sci-bots/dropbot-v3/docs/images/png/MicroDrop screenshots/MicroDrop left pane - green.png

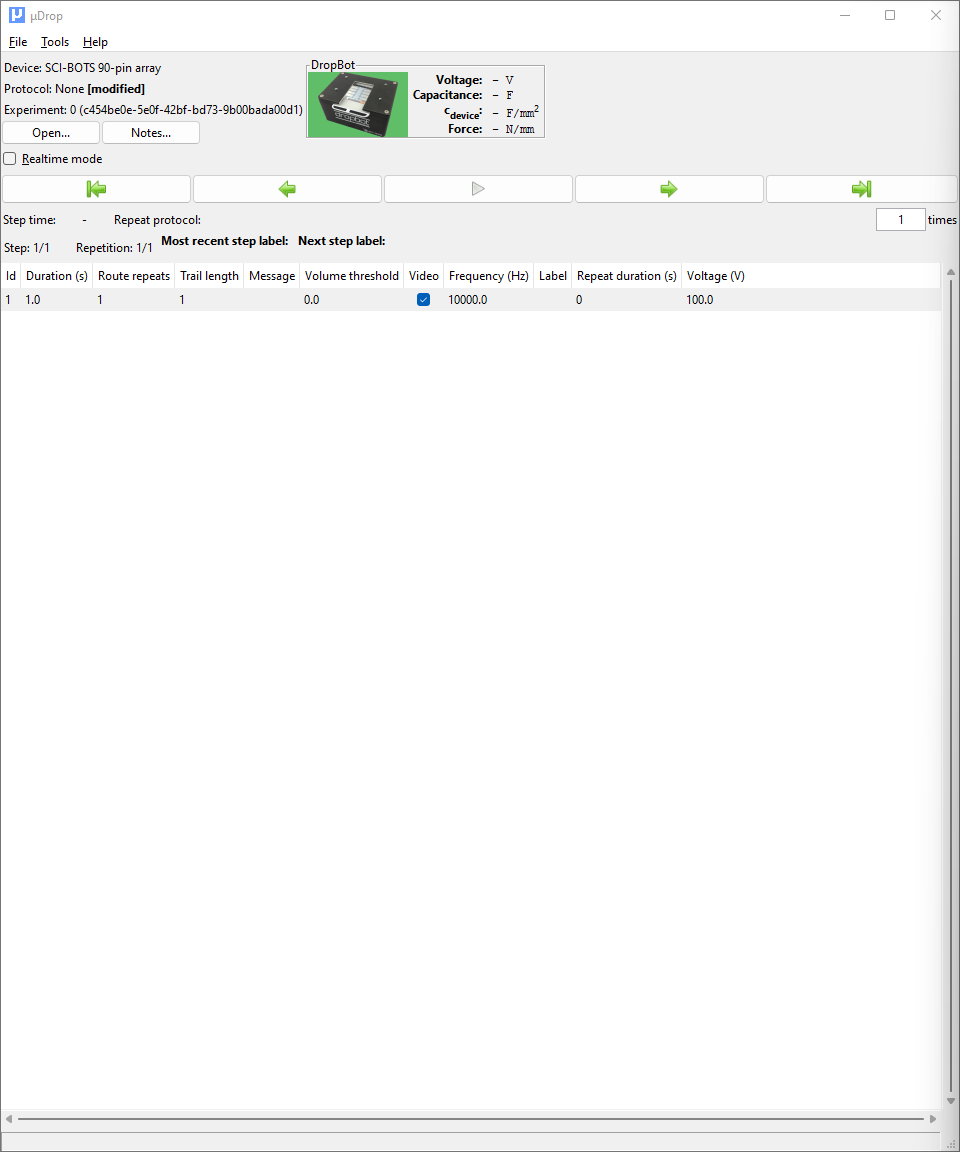
docs/images/png/MicroDrop screenshots/MicroDrop left pane - green.png
