sci-bots/dropbot-v3/docs/images/png/MicroDrop screenshots/MicroDrop left pane - yellow.png

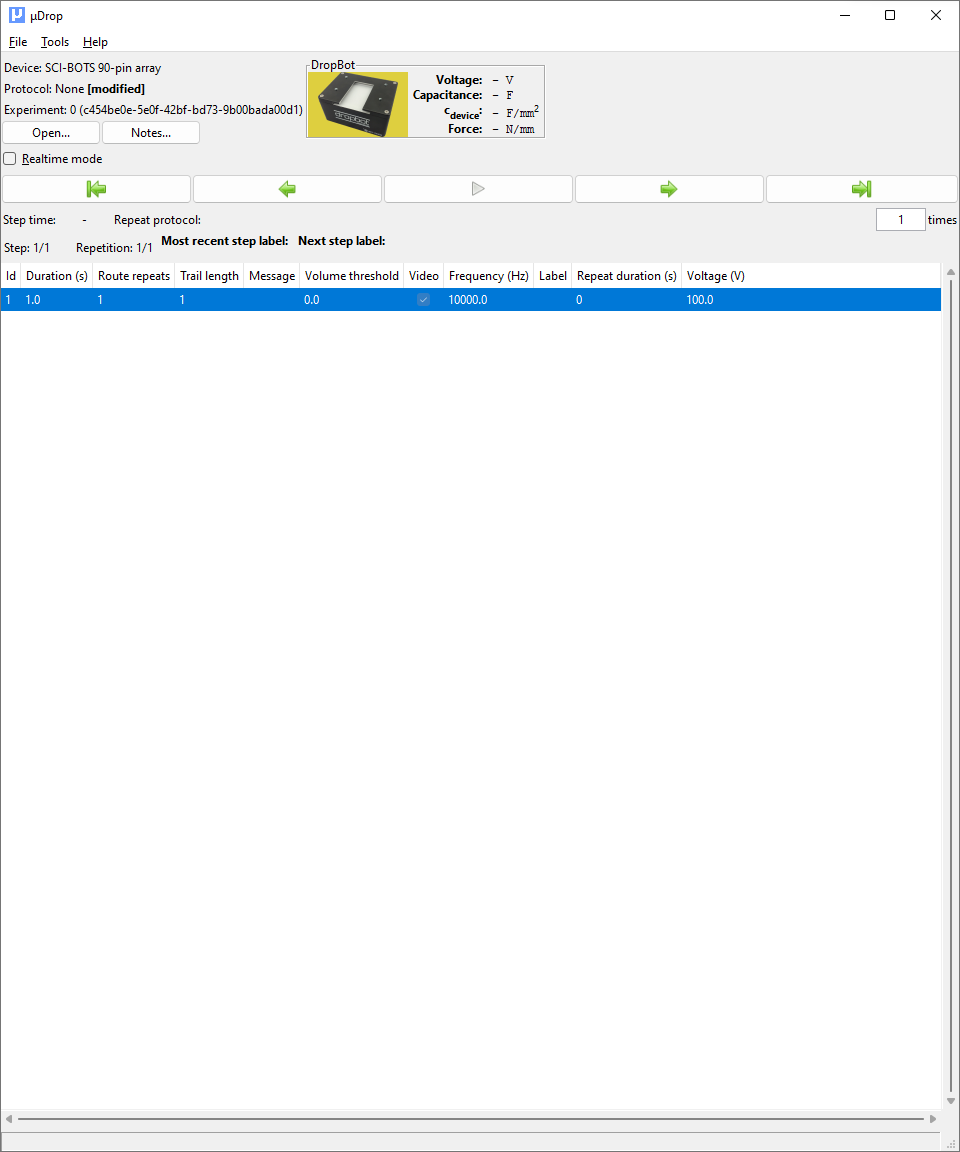
docs/images/png/MicroDrop screenshots/MicroDrop left pane - yellow.png
