sci-bots/dropbot-v3/docs/images/png/MicroDrop screenshots/Teensy1.png

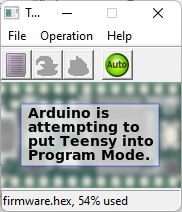
docs/images/png/MicroDrop screenshots/Teensy1.png
