sci-bots/dropbot-v3/docs/images/png/MicroDrop screenshots/Teensy2.png

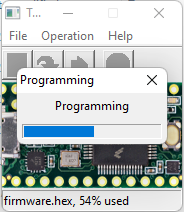
docs/images/png/MicroDrop screenshots/Teensy2.png
