sci-bots/dropbot-v3/docs/images/png/MicroDrop screenshots/Teensy3.png

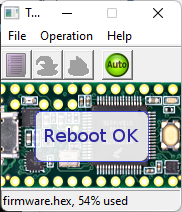
docs/images/png/MicroDrop screenshots/Teensy3.png
