sci-bots/dropbot-v3/docs/images/jpg/Assembly pictures/PXL_20220801_192833574.jpg

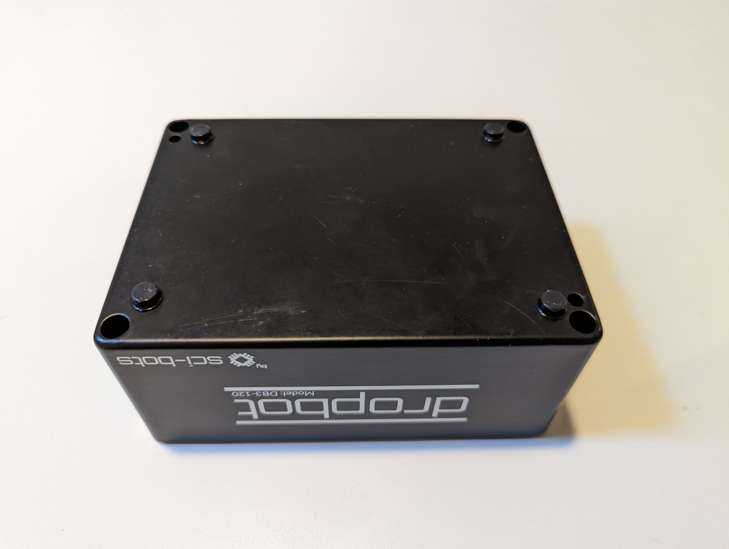
docs/images/jpg/Assembly pictures/PXL_20220801_192833574.jpg
