sci-bots/dropbot-v3/docs/images/jpg/Assembly pictures/PXL_20220801_195305338.jpg

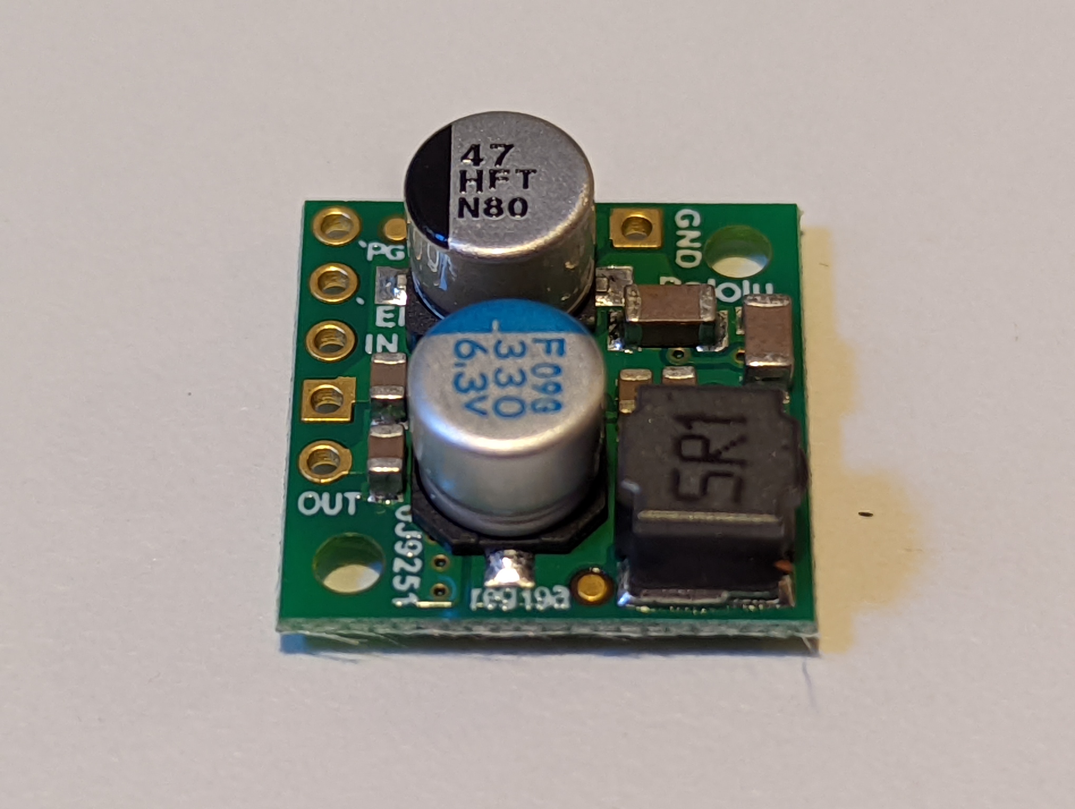
docs/images/jpg/Assembly pictures/PXL_20220801_195305338.jpg
