sci-bots/dropbot-v3/docs/images/jpg/Assembly pictures/PXL_20220801_195425001.jpg

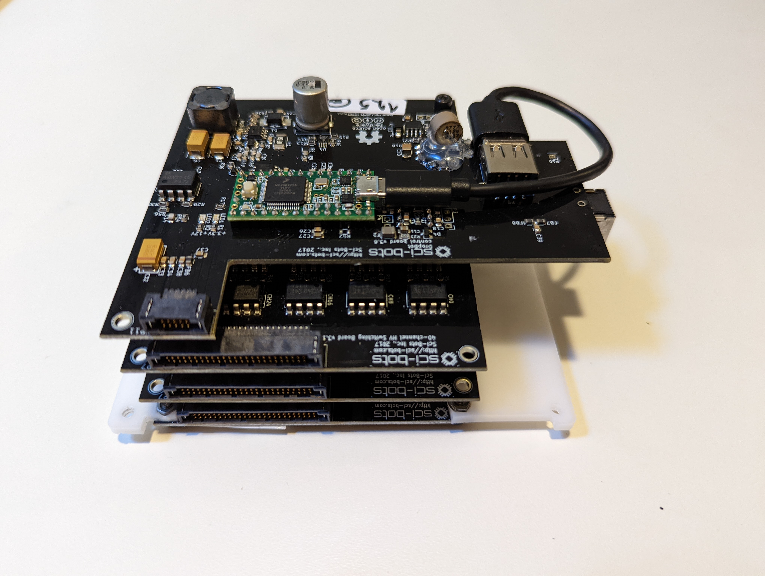
docs/images/jpg/Assembly pictures/PXL_20220801_195425001.jpg
