sci-bots/dropbot-v3/docs/images/jpg/Assembly pictures/PXL_20220801_200302027.jpg

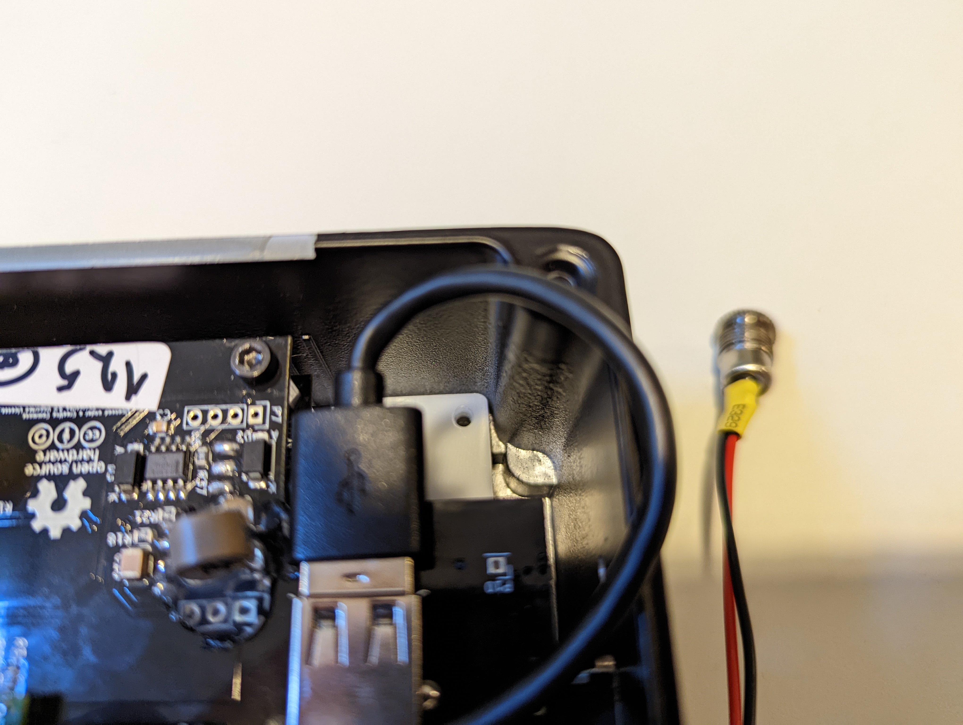
docs/images/jpg/Assembly pictures/PXL_20220801_200302027.jpg
