sci-bots/dropbot-v3/docs/images/jpg/Assembly pictures/PXL_20220801_200440907_circle.jpg

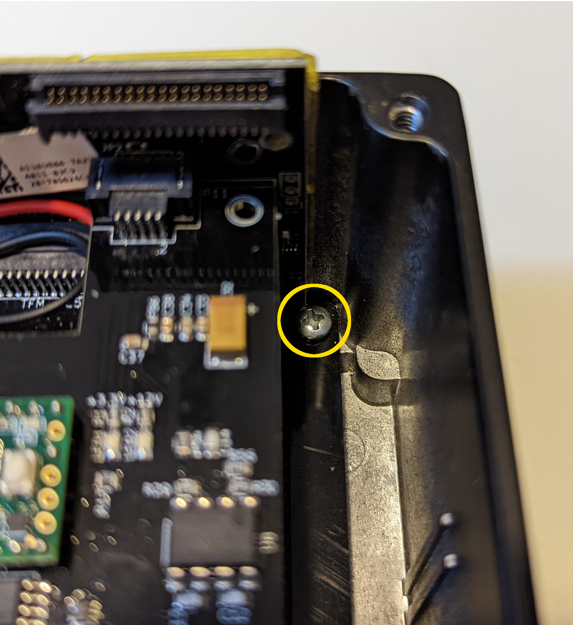
docs/images/jpg/Assembly pictures/PXL_20220801_200440907_circle.jpg
