sci-bots/dropbot-v3/docs/images/jpg/Assembly pictures/PXL_20220801_200446743_circle.jpg

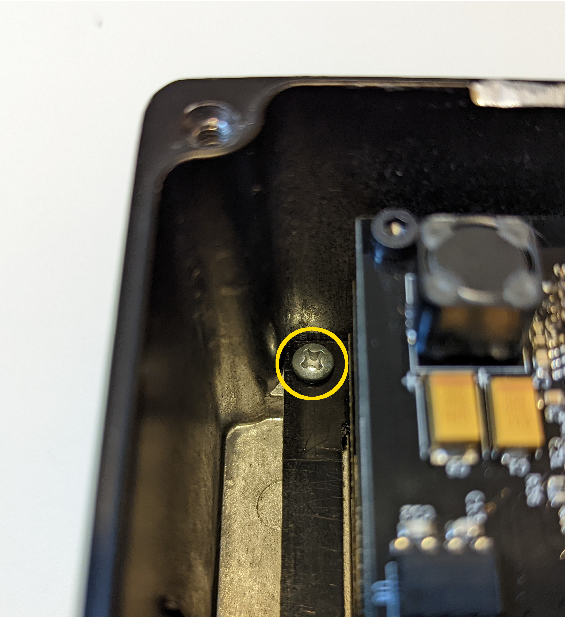
docs/images/jpg/Assembly pictures/PXL_20220801_200446743_circle.jpg
