sci-bots/dropbot-v3/docs/images/jpg/Assembly pictures/PXL_20220801_200449386.jpg

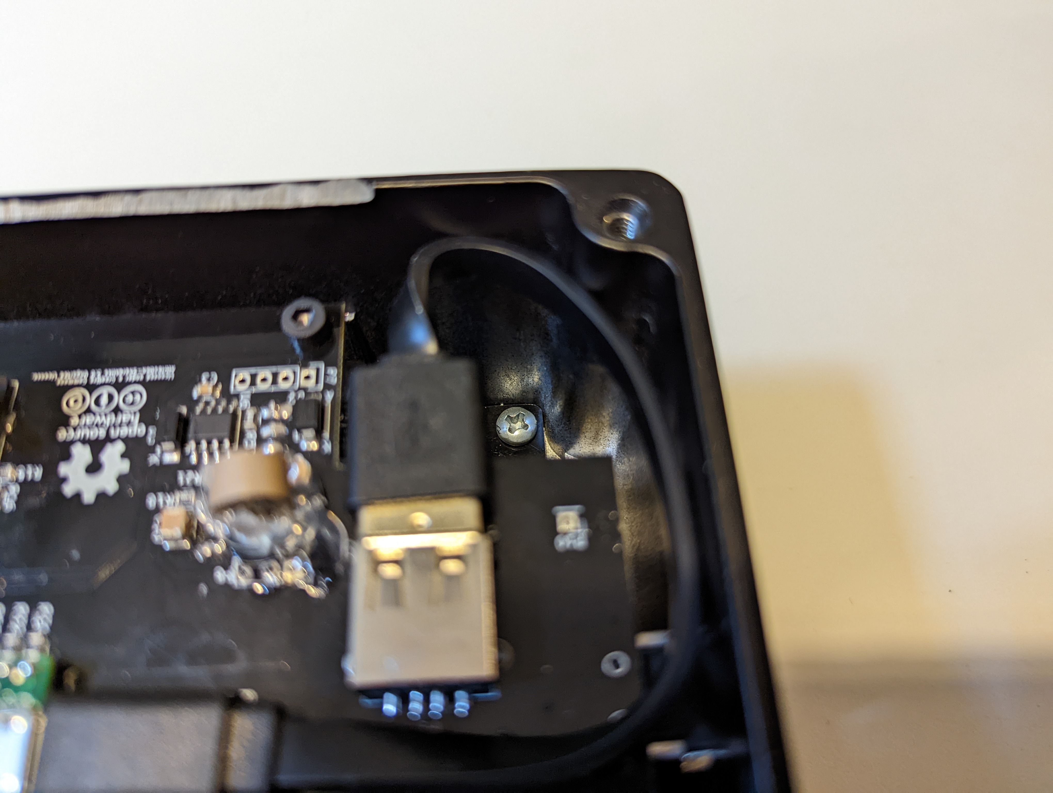
docs/images/jpg/Assembly pictures/PXL_20220801_200449386.jpg
