sci-bots/dropbot-v3/docs/images/jpg/Assembly pictures/PXL_20220801_200946529.jpg

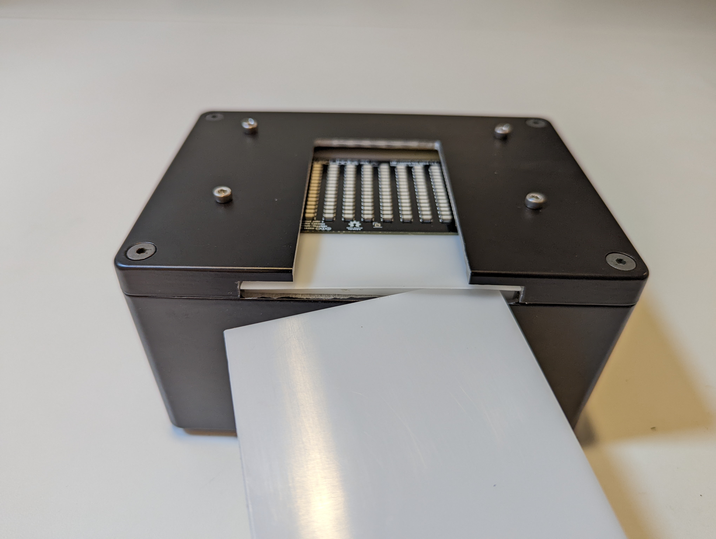
docs/images/jpg/Assembly pictures/PXL_20220801_200946529.jpg
