sci-bots/dropbot-v3/docs/images/jpg/Assembly pictures/PXL_20220801_202122598.jpg

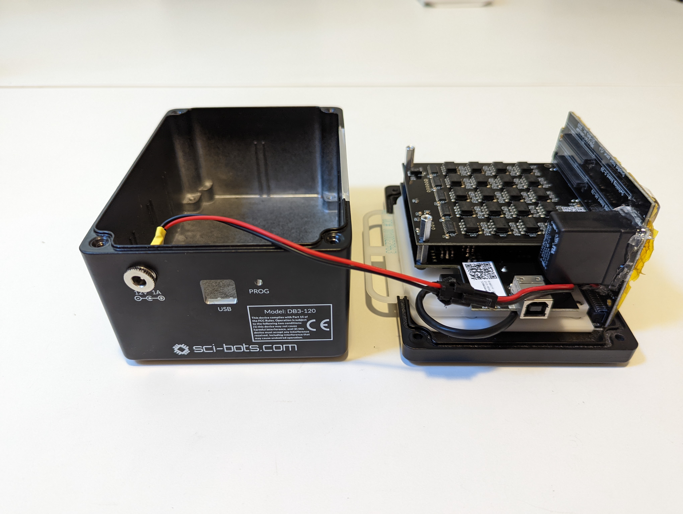
docs/images/jpg/Assembly pictures/PXL_20220801_202122598.jpg
