sci-bots/dropbot-v3/docs/images/jpg/Assembly pictures/PXL_20220801_202247939.jpg

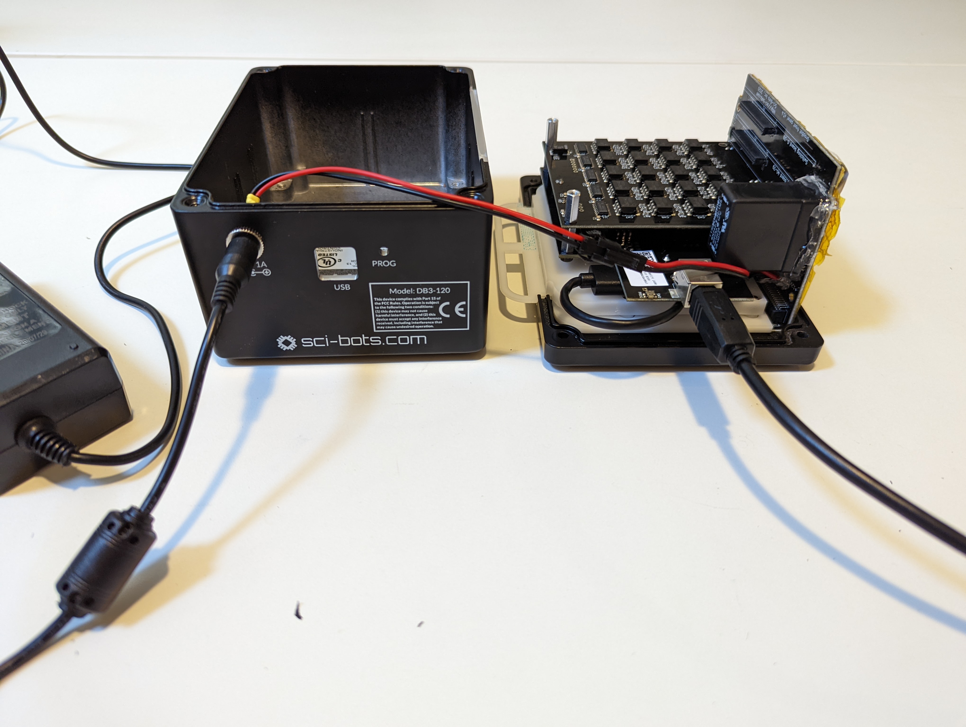
docs/images/jpg/Assembly pictures/PXL_20220801_202247939.jpg
