sci-bots/dropbot-v3/docs/images/png/MicroDrop screenshots/Self tests.png

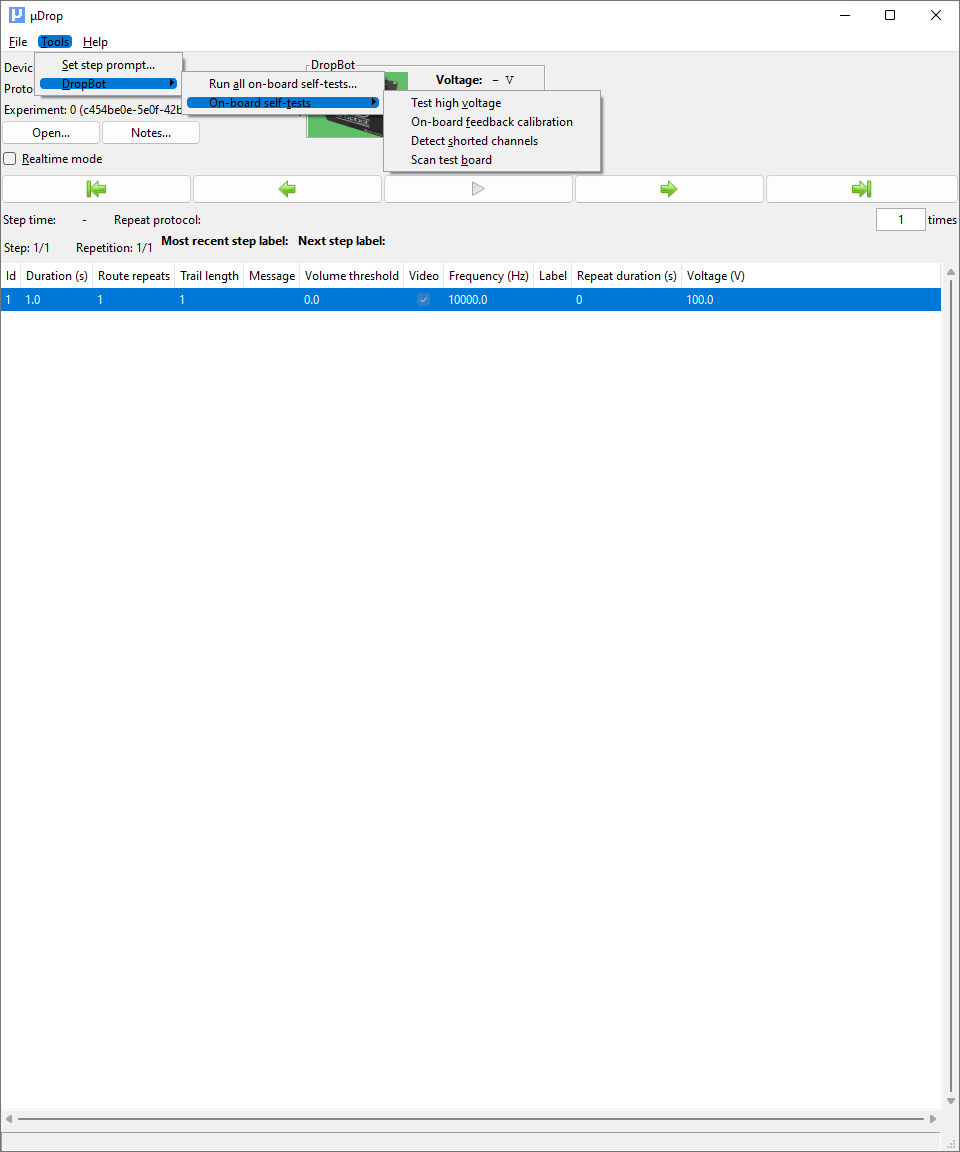
docs/images/png/MicroDrop screenshots/Self tests.png
