sci-bots/dropbot-v3/docs/images/png/results-summary_1.png

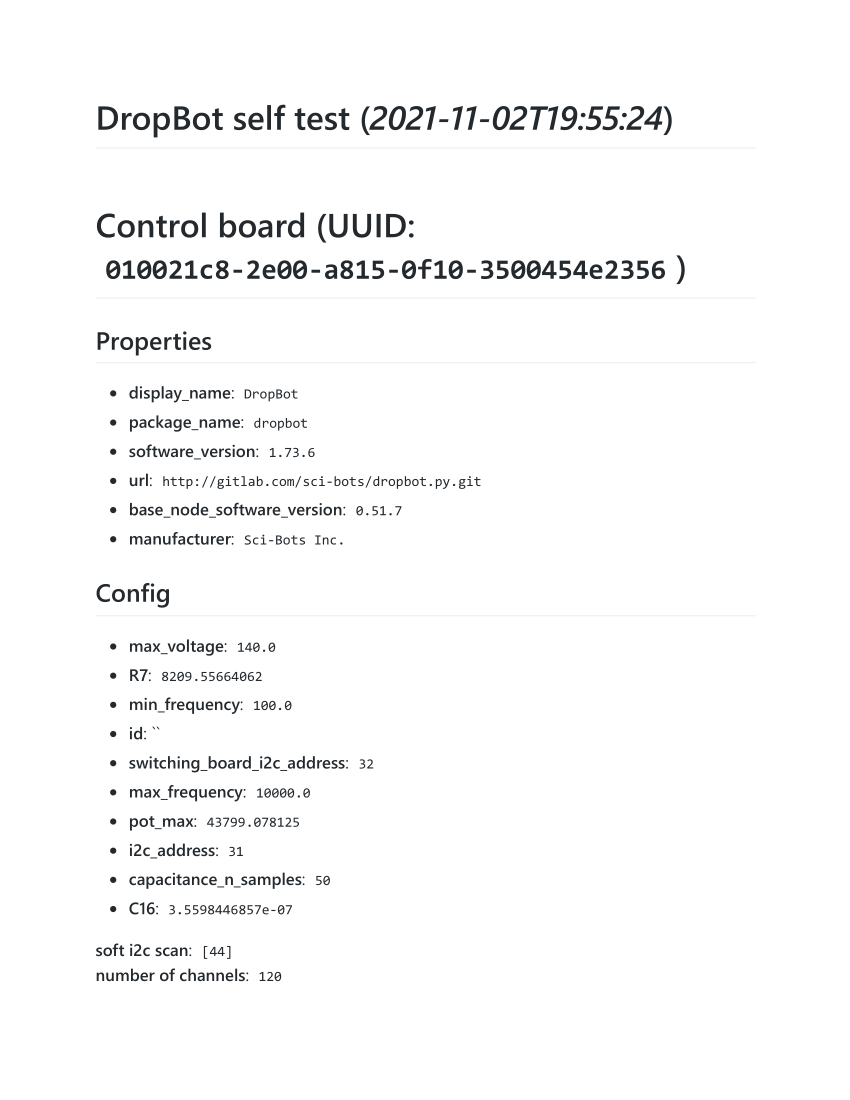
docs/images/png/results-summary_1.png
