sci-bots/dropbot-v3/docs/images/png/results-summary_2.png

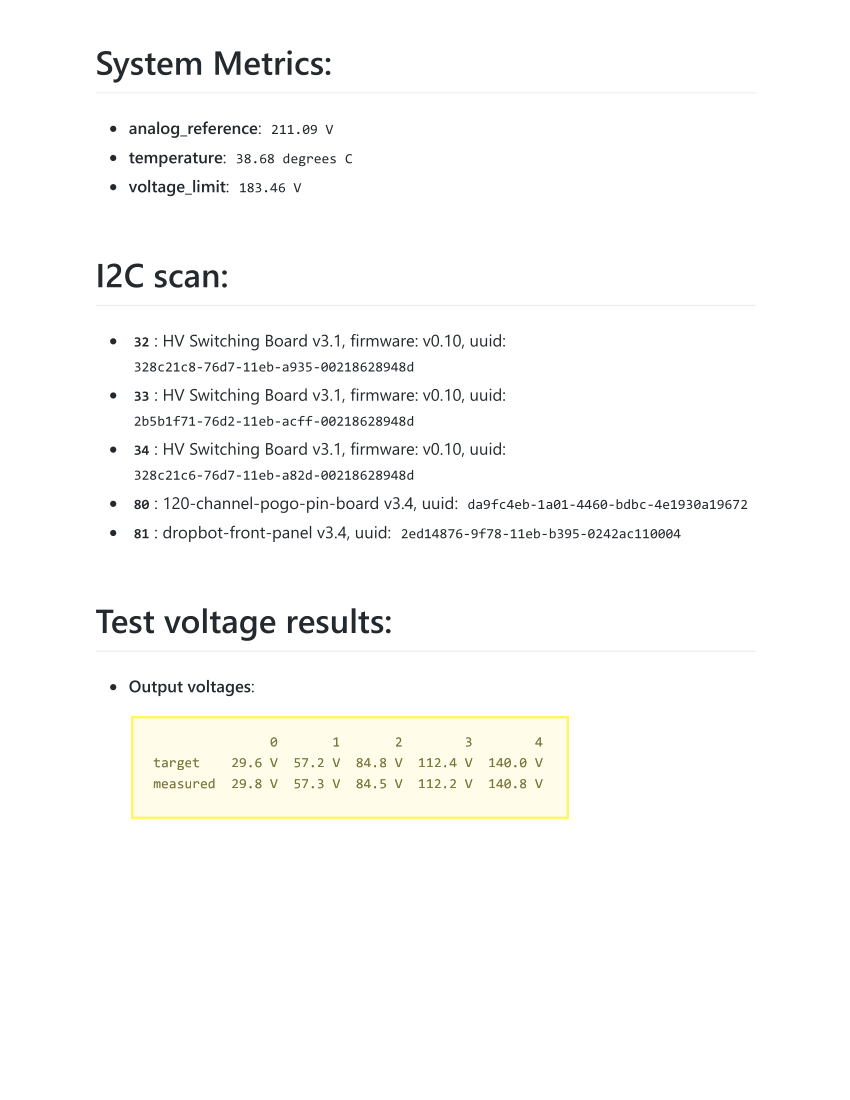
docs/images/png/results-summary_2.png
