sci-bots/dropbot-v3/docs/images/png/results-summary_3.png

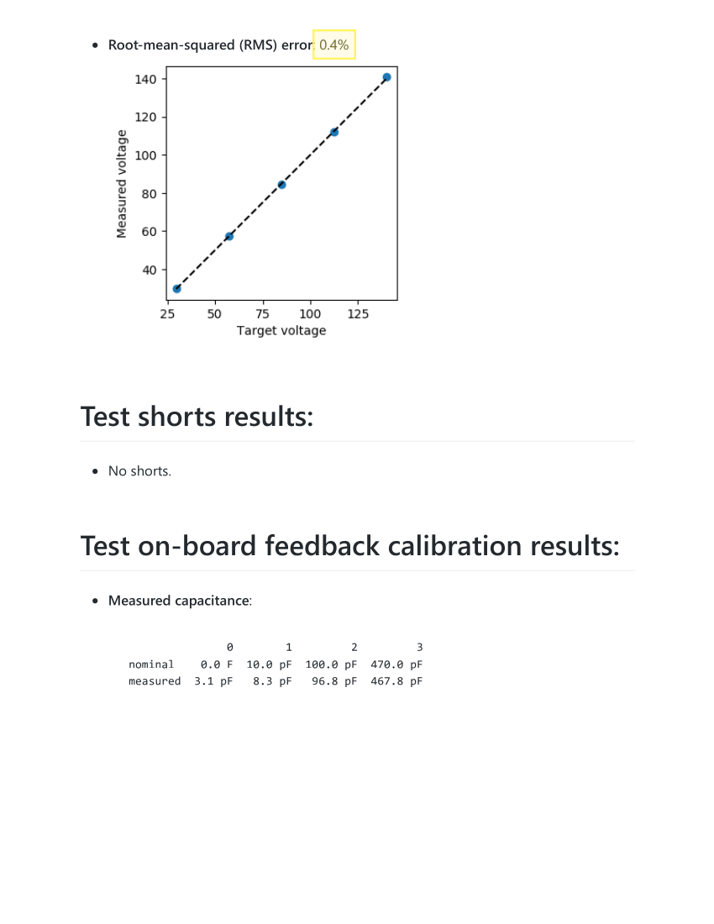
docs/images/png/results-summary_3.png
