sci-bots/dropbot-v3/docs/images/png/results-summary_4.png

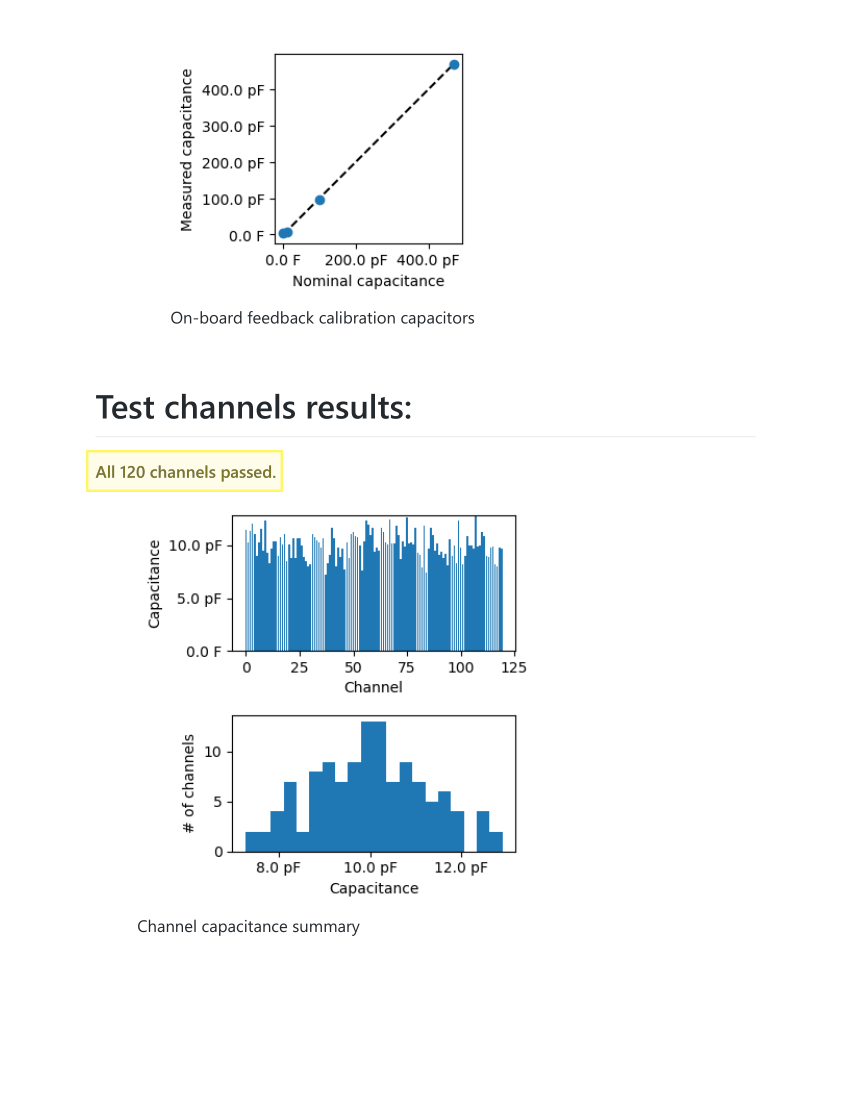
docs/images/png/results-summary_4.png
